danielz-yu/ECE499_Thesis_BRI_PRISM_Lab/enclosure_design_cad/renders/Electrode Case Cap.png

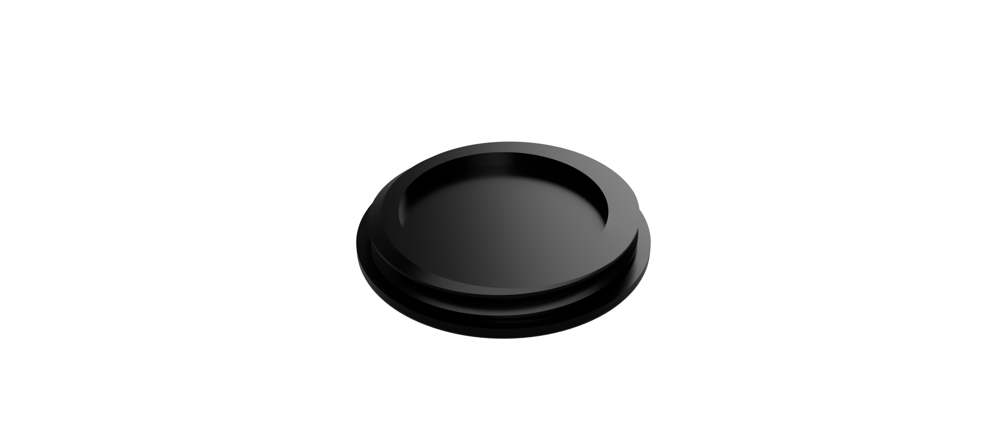
enclosure_design_cad/renders/Electrode Case Cap.png
